Vitech-UA/WiFi-Router-UPS/MEDIA/20251227_003443.jpg

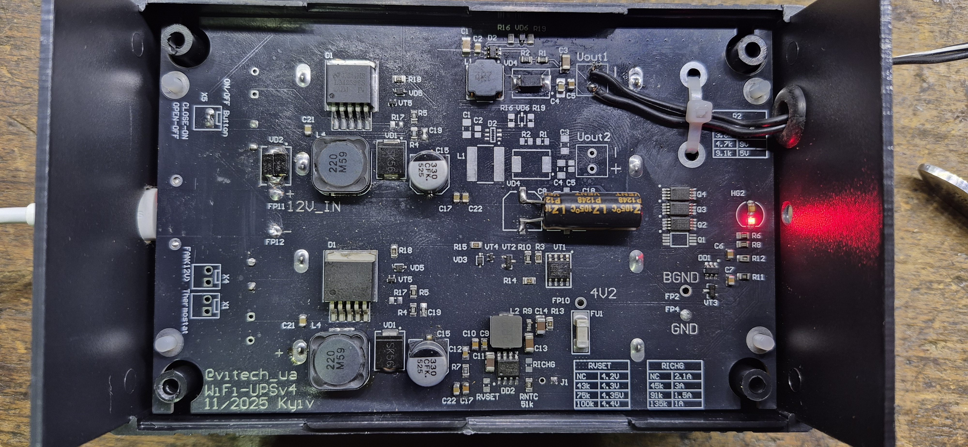
MEDIA/20251227_003443.jpg
