Vitech-UA/WiFi-Router-UPS/MEDIA/20251227_111137.jpg

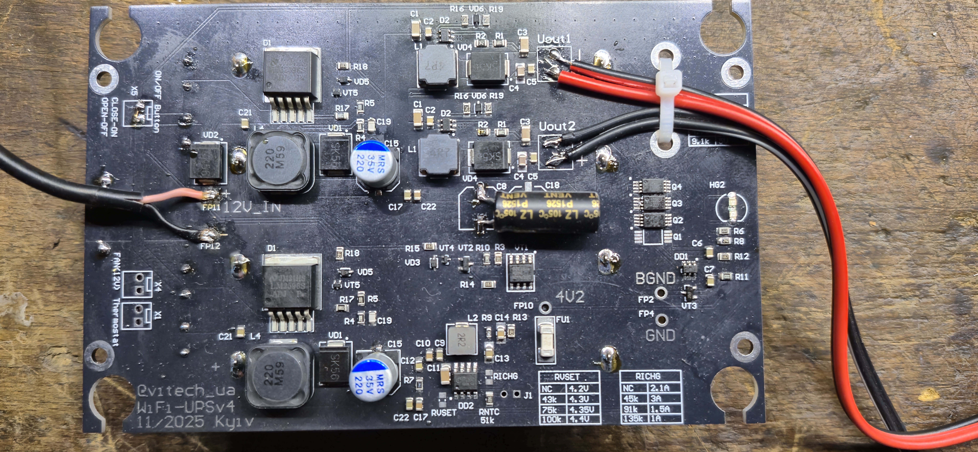
MEDIA/20251227_111137.jpg
