Vitech-UA/WiFi-Router-UPS/MEDIA/20251227_114001.jpg

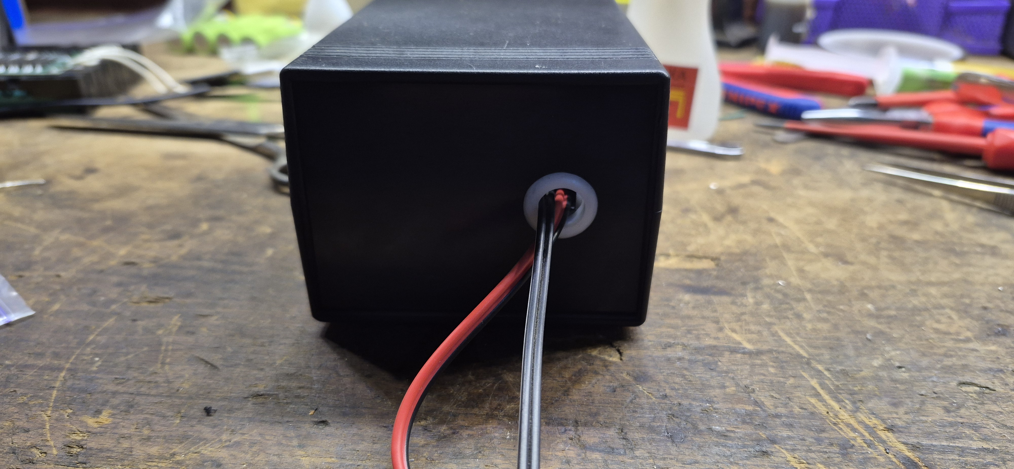
MEDIA/20251227_114001.jpg
