Vitech-UA/WiFi-Router-UPS/MEDIA/20251227_114006.jpg

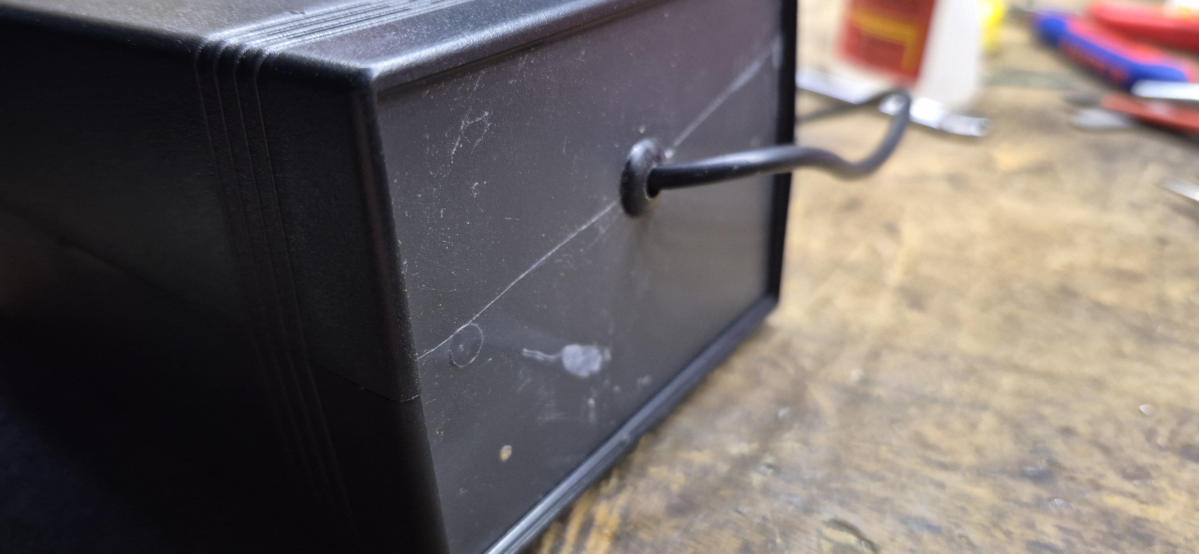
MEDIA/20251227_114006.jpg
